themkoi/NordiCoin/other/light_button/src/other.rs

use crate::prelude::*;

pub trait Log<T> {
    fn log(&self);
}

impl<T, E> Log<T> for Result<T, E>
where
    E: Format,
{
    fn log(&self) {
        if let Err(e) = self {
            error!("{:?}", e);
        }
    }
    /*
    fn log_ms(self, msg: &str) {
        if let Err(e) = self {
            error!("{}: {:?}", msg, e);
        }
    }
    */
}
