themkoi/NordiCoin/other/light_button/src/no_debug.rs

#[macro_export]
macro_rules! info {
    ($($arg:tt)+) => {};
}
#[macro_export]
macro_rules! debug {
    ($($arg:tt)+) => {};
}
#[macro_export]
macro_rules! warn {
    ($($arg:tt)+) => {};
}
#[macro_export]
macro_rules! error {
    ($($arg:tt)+) => {};
}
#[macro_export]
macro_rules! trace {
    ($($arg:tt)+) => {};
}
